ahmadq122/Digital-Weighing-Scale-6-Channel-MQTT/kicad/kicad-weight-scale-6-ch-rev_1.1-1.0/png/INALAB-full-wh.png

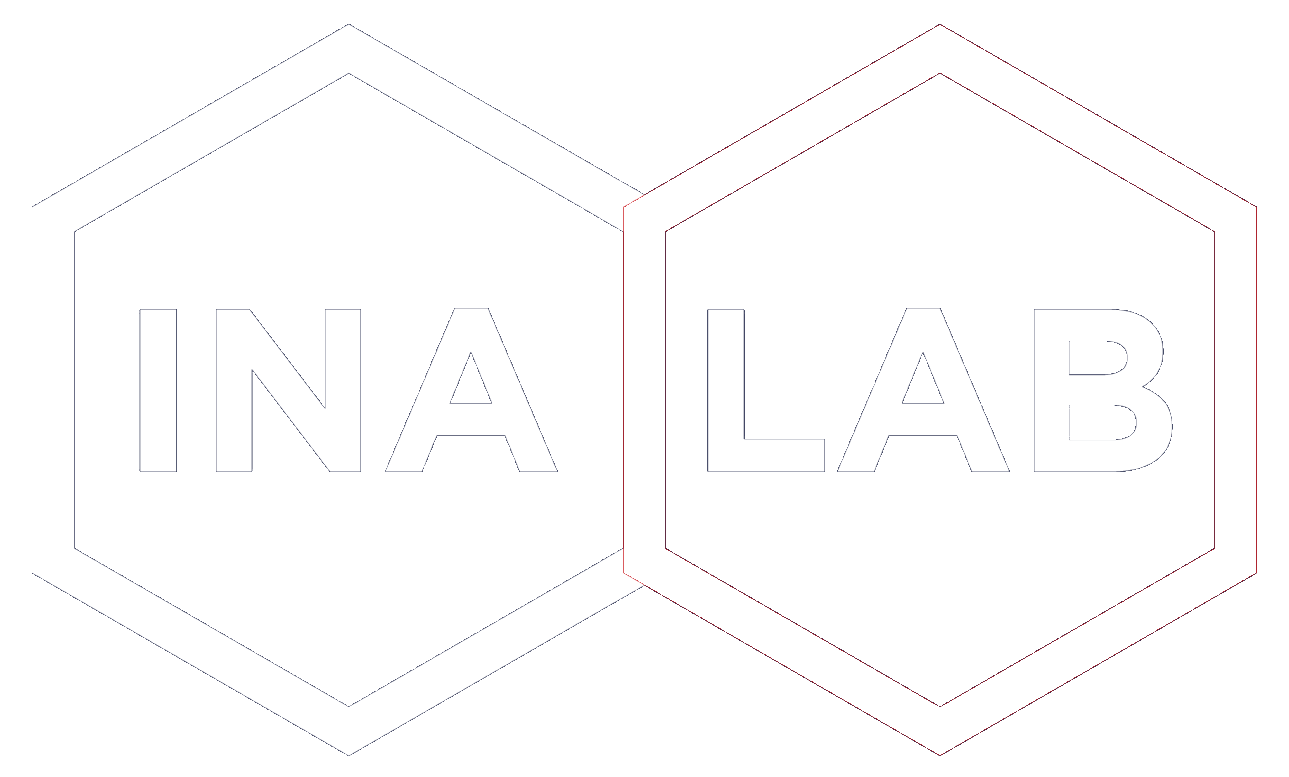
kicad/kicad-weight-scale-6-ch-rev_1.1-1.0/png/INALAB-full-wh.png
