ahmadq122/Digital-Weighing-Scale-6-Channel-MQTT/kicad/kicad-weight-scale-6-ch-rev_1.1-1.0/png/kicad-weight-scale-6-ch_top.png

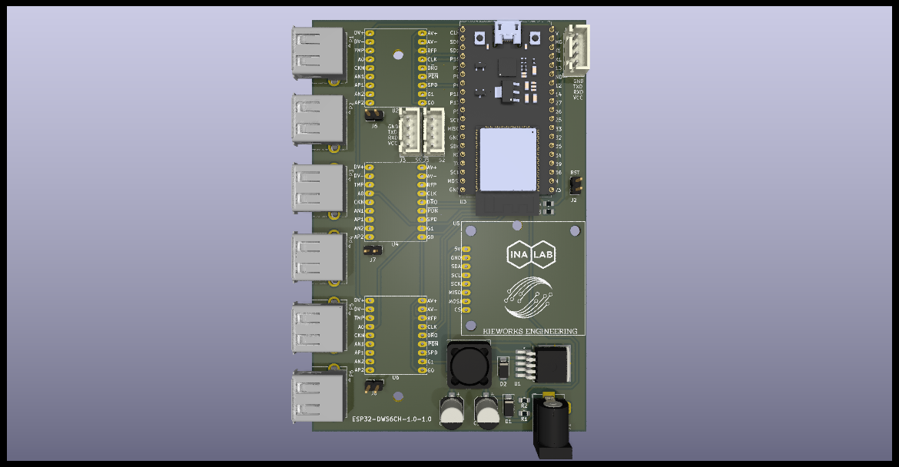
kicad/kicad-weight-scale-6-ch-rev_1.1-1.0/png/kicad-weight-scale-6-ch_top.png
