ahmadq122/Digital-Weighing-Scale-6-Channel-MQTT/src/Network/Network.cpp

#include "Network.h"
#include <WiFi.h>
#include "../FlashMemory/FlashMemory.h"
#include "../Nextion/Nextion.h"
#include "RTOS/RTOS.h"
#include "PictureListID.h"
#include "Utility/Utility.h"

void Network::setup(void)
{
    // Set WiFi to station mode and disconnect from an AP if it was previously connected
    // fdata->readAll();
    WiFi.mode(WIFI_STA);
    WiFi.disconnect();
    delay(100);
    if (fdata->getNetworkEnable())
    {
        WiFi.begin(fdata->getSSID(), fdata->getPassword());
        // WiFi.setAutoReconnect(true);
    }
    // Serial.println("Wifi Setup done");
}

const char *getStringEncrypt(byte parameter)
{
    if (parameter == 0)
        return "OPEN";
    else if (parameter == 1)
        return "WEP";
    else if (parameter == 2)
        return "WPA_PSK";
    else if (parameter == 3)
        return "WPA2_PSK";
    else if (parameter == 4)
        return "WPA_WPA2_PSK";
    else if (parameter == 5)
        return "WPA2_ENTERPRISE";
    else if (parameter == 6)
        return "MAX";
    else
        return "UNKNOWN";
}

char *getIPAdderss(void)
{
    static char buffer[30];
    // String ip;
    sprintf(buffer, "%s.%s.%s.%s", String(WiFi.localIP()[0]).c_str(), String(WiFi.localIP()[1]).c_str(), String(WiFi.localIP()[2]).c_str(), String(WiFi.localIP()[3]).c_str());
    // ip = String() + WiFi.localIP()[0] + "." + WiFi.localIP()[1] + "." + WiFi.localIP()[2] + "." + WiFi.localIP()[3];
    return buffer;
}

char *getStringPasswordMask(const char *string)
{
    char buffer[20];
    strcpy(buffer, string);
    // String str = string;
    uint8_t length = 0; // str.length();
    uint8_t i = 0;
    while (buffer[i] != '\0')
    {
        length++;
        i++;
    }

    static char mask[20];
    for (i = 0; i < length; i++)
        mask[i] = '*';
    mask[length] = '\0';
    return mask;
}

void Network::showNetworkProperty(bool flag)
{
    char buffer[50];
    if (flag)
    {
        for (uint8_t i = 1; i <= 6; i++)
        {
            sprintf(buffer, "q%d", i);
            hmi->setVisObjectNextion(buffer, true);
            sprintf(buffer, "t%d", i);
            hmi->setVisObjectNextion(buffer, true);
            delay(20);
            sprintf(buffer, "t%d.txt", i);
            if (i == 1)
            {
                hmi->setStringToNextion(buffer, WiFi.isConnected() ? "Connected" : "Unconnected");
            }
            else if (i == 2)
            {
                hmi->setStringToNextion(buffer, fdata->getSSID());
            }
            else if (i == 3)
            {
                hmi->setStringToNextion(buffer, utils.integerToString(WiFi.RSSI()));
            }
            else if (i == 4)
            {
                hmi->setStringToNextion(buffer, getIPAdderss());
            }
            else if (i == 5)
            {
                hmi->setStringToNextion(buffer, getStringEncrypt(fdata->getEncryptType()));
            }
            else if (i == 6)
            {
                hmi->setStringToNextion(buffer, getStringPasswordMask(fdata->getPassword()));
            }
        }
    }
    else
    {
        for (uint8_t i = 1; i <= 6; i++)
        {
            sprintf(buffer, "q%d", i);
            hmi->setVisObjectNextion(buffer, false);
            sprintf(buffer, "t%d", i);
            hmi->setVisObjectNextion(buffer, false);
        }
    }
}

bool Network::networkConfig(void)
{
    uint8_t button;
    bool netEnDis = false;
    bool needToRefreshStatus = false;

    hmi->showPage("netconf");
    hmi->waitForPageRespon();

    netEnDis = fdata->getNetworkEnable();

    hmi->setIntegerToNextion("b1.val", netEnDis);

    while (!hmi->getExitPageFlag())
    {
        if (!WiFi.isConnected() && netEnDis)
        {
            needToRefreshStatus = true;
            WiFi.begin(fdata->getSSID(), fdata->getPassword());
            // Serial.println(String() + "Connecting to " + fdata->getSSID());
        }
        if (fdata->getNetworkEnable())
        {
            hmi->setVisObjectNextion("b2", true);
            showNetworkProperty(true);
        }
        else
        {
            hmi->setVisObjectNextion("b2", false);
            showNetworkProperty(false);
        }
        // Wait for button press
        while (!hmi->checkAnyButtonPressed(&button))
        {
            // hmi->serialEvent_2();
            // delay(10);
            if (needToRefreshStatus && (WiFi.isConnected()))
            {
                showNetworkProperty(true);
                needToRefreshStatus = false;
            }
        }
        if (hmi->getDataButton(1))
        {
            netEnDis = !netEnDis;
            fdata->setNetworkEnable(netEnDis);
            hmi->setIntegerToNextion("b1.val", netEnDis);
            if (!netEnDis)
            {
                if (WiFi.isConnected())
                {
                    WiFi.disconnect();
                    // Serial.println("Network disconnected!");
                }
            }
        }
        else if (hmi->getDataButton(2))
        {
            return true;
        }
    }
    return false; // entering the scanning page;
}

void Network::networkScanning(void)
{
    uint8_t counterScan = 0;
    String ssidScanned[3][10];
    int rssiScanned[3][10];
    uint8_t encryptType[3][10];
    uint8_t numberOfNetworkFound[3];
    uint8_t selectedScan = 0, prevNoScan = 0;
    uint8_t progress = 0;
    String str;
    uint8_t button;
    char buffer[30];

    hmi->showPage("netscan");
    hmi->waitForPageRespon();
    // Serial.println("Network Scan page opened");
    WiFi.mode(WIFI_STA);
    WiFi.disconnect();

__scan:
    hmi->setIntegerToNextion("scan.val", progress);
    hmi->setVisObjectNextion("scan", true);
    counterScan = 0;
    while (counterScan < 3)
    {
        progress += 15;
        hmi->setIntegerToNextion("scan.val", progress);
        numberOfNetworkFound[counterScan] = WiFi.scanNetworks();
        for (uint8_t i = 0; i < numberOfNetworkFound[counterScan]; i++)
        {
            ssidScanned[counterScan][i] = WiFi.SSID(i);
            rssiScanned[counterScan][i] = WiFi.RSSI(i);
            encryptType[counterScan][i] = WiFi.encryptionType(i);
        }
        delay(2000);
        progress += 15;
        hmi->setIntegerToNextion("scan.val", progress);
        selectedScan = prevNoScan >= numberOfNetworkFound[counterScan] ? selectedScan : counterScan;
        prevNoScan = numberOfNetworkFound[counterScan];
        counterScan++;
        delay(1000);
    }

    delay(250);
    progress = 100;
    hmi->setIntegerToNextion("scan.val", progress);
    delay(250);
    hmi->setVisObjectNextion("scan", false);

    hmi->flushAvailableSerial();

    if (numberOfNetworkFound[selectedScan] == 0)
    {
        hmi->setStringToNextion("nonet.txt", "No Network Found!");
        hmi->setVisObjectNextion("nonet", true);
        // Serial.println("No network found!");
        while (!hmi->getExitPageFlag())
        {
            while (!hmi->checkAnyButtonPressed(&button))
            {
            }
            if (hmi->getDataButton(0))
            {
                hmi->setVisObjectNextion("nonet", false);
                progress = 0;
                goto __scan;
            }
        }
    }
    else
    {
        showNetworkList(numberOfNetworkFound[selectedScan]);
        // Serial.println(String() + numberOfNetworkFound[selectedScan] + " Networks found");
        while (!hmi->getExitPageFlag())
        {
            for (int i = 0; i < numberOfNetworkFound[selectedScan]; ++i)
            {
                if (isStoredNetwork(ssidScanned[selectedScan][i].c_str()))
                    showSelectedNetworkIndicator(i, numberOfNetworkFound[selectedScan]);
                str = ssidScanned[selectedScan][i];
                str += ":";
                str += rssiScanned[selectedScan][i];
                // Serial.println(String() + (i + 1) + ". " + str);
                sprintf(buffer, "b%d.txt", i);
                hmi->setStringToNextion(buffer, str.c_str());
            }
            while (!hmi->checkAnyButtonPressed(&button))
            {
                // hmi->serialEvent_2();
                // //Serial.println("wait1");
            }

            if (hmi->getDataButton(button))
            {
                if (ssidScanned[selectedScan][button].length() < MAX_SSID_CHAR)
                {
                    if (fdata->setSSID(ssidScanned[selectedScan][button].c_str()))
                    {
                        showSelectedNetworkIndicator(button, numberOfNetworkFound[selectedScan]);
                        fdata->setEncryptType(encryptType[selectedScan][button]);
                        WiFi.mode(WIFI_STA);
                        WiFi.disconnect();
                        delay(100);
                    }
                    rtos->wifiConnected = checkConnection();
                    if (!rtos->wifiConnected)
                    {
                        hmi->showPage("keyboard");
                        hmi->waitForPageRespon();
                        hmi->setIntegerToNextion("kb_hide.val", 1);
                        hmi->setIntegerToNextion("kb_string.pw", 1);

                        button = 0;
                        while (!hmi->checkAnyButtonPressed(&button))
                        {
                        }
                        if (hmi->getDataButton(1))
                        {
                            fdata->setPassword(hmi->getDataString(0));
                        }
                        hmi->showPage("netscan");
                        hmi->waitForPageRespon();
                        showNetworkList(numberOfNetworkFound[selectedScan]);
                    }
                }
                else
                {
                    // char* nonet = "No Network Found";
                    hmi->setStringToNextion("nonet.txt", "Invalid SSID!");
                    hmi->setVisObjectNextion("nonet", true);
                    delay(2000);
                    hmi->setVisObjectNextion("nonet", false);
                    // Serial.println("SSID selected must be no more than 11 characters!");
                }
            }
        }
    }
}

void Network::showNetworkList(uint8_t noOfList)
{
    char buffer[10];
    if (noOfList > 10)
        return;
    for (uint8_t i = 0; i < noOfList; i++)
    {
        sprintf(buffer, "b%d", i);
        hmi->setVisObjectNextion(buffer, true);
    }
    delay(500);
}

void Network::showSelectedNetworkIndicator(uint8_t selected, uint8_t noOfList)
{
    char buffer[20];
    if (noOfList > 10)
        return;
    sprintf(buffer, "b%d.picc", selected);
    hmi->setIntegerToNextion(buffer, Network_List_Select);
    for (uint8_t i = 0; i < noOfList; i++)
    {
        if (i == selected)
            continue;
        else
        {
            sprintf(buffer, "b%d.picc", i);
            hmi->setIntegerToNextion(buffer, Network_List_Bkg);
        }
    }
}

bool Network::isStoredNetwork(const char *networkName)
{
    if (!strcmp(networkName, fdata->getSSID()))
        return true;
    else
        return false;
}

bool Network::checkConnection(void)
{
    String ssid = fdata->getSSID();
    String password = fdata->getPassword();
    uint8_t counter = 0;
    if (ssid == "" || password == "")
    {
        return false;
    }

    if (!fdata->getNetworkEnable())
    {
        return false;
    }

    if (WiFi.isConnected())
    {
        // Serial.println("Network connected!");
    }
    else
    {
        // Serial.println("Network connection failed!");
        WiFi.begin(fdata->getSSID(), fdata->getPassword());
        while (!WiFi.isConnected() && counter <= 10)
        {
            delay(100);
            counter++;
        }
        if (WiFi.isConnected())
        {
            // Serial.println("Network connected!");
        }
    }
    return WiFi.isConnected();
}

bool Network::checkConnection(uint8_t *wifiSignal, bool *wifiConnectionTriggered)
{
    String ssid = fdata->getSSID();
    String password = fdata->getPassword();
    if (ssid == "" || password == "")
    {
        return false;
        // fdata->readAll();
    }

    bool connection = false;

    if (!fdata->getNetworkEnable())
    {
        *wifiSignal = 0;
        *wifiConnectionTriggered = false;
        return false;
    }

    if (WiFi.isConnected())
    {
        connection = true;
        *wifiSignal = calculateRSSILevel(WiFi.RSSI());
        if (*wifiConnectionTriggered && previousConnectionState != true)
        {
            previousConnectionState = true;
            // Serial.println("Network connected!");
        }
    }
    else
    {
        *wifiSignal = 0;
        connection = false;
        if (*wifiConnectionTriggered && previousConnectionState != false)
        {
            previousConnectionState = false;
            // Serial.println("Network connection failed!");
        }
    }
    if (*wifiConnectionTriggered)
    {
        if (!connection)
        {
            WiFi.begin(fdata->getSSID(), fdata->getPassword());
        }
        *wifiConnectionTriggered = false;
    }
    return connection;
}
uint8_t Network::calculateRSSILevel(int value)
{
    if (value >= -50)
        return 100;
    else if (value >= -60)
        return 85;
    else if (value >= -70)
        return 65;
    else if (value >= -80)
        return 45;
    else if (value >= -95)
        return 25;
    else
        return 0;
}

Network *net = new (Network);
