ahmadq122/Digital-Weighing-Scale-6-Channel-MQTT/src/ADC/ADS1232.h

#ifndef _ADS1232_H_
#define _ADS1232_H_

#include "Arduino.h"

#define SAMPLE_MOV_AVERAGE 40
#define ADC_OFFSET 100

#ifndef MAX_CHANNEL
#define MAX_CHANNEL 6
#endif

#define ERROR_WEIGHT 9999.999

enum Channel
{
    Channel1,
    Channel2,
    Channel3,
    Channel4,
    Channel5,
    Channel6
};
enum MeasurementUnits
{
    gram,       //1g
    milligram,  //1mg   = (1/0.001)g
    pound,      //1lb   = (1/453.59237)g
    ounce,      //1oz   = (1/28.34952)g
    troy_ounce, //1ozt  = (1/31.1034768)g
    carat,      //1ct   = (1/0.2)g
    kilogram,   //1kg   = (1/1000)g
    newton,     //1N    = (1/0.009807)g
    dram,       //1d    = (1/0.564383)g
    grain       //1GN   = (1/15.43236)g
};

enum BoardADS
{
    ads1,
    ads2,
    ads3
};

class ADS1232
{
public:
    uint32_t adcRead[3][2];     //ADC value after filtered
    String adcReadString[3][2]; ////ADC value convert to 10 characters of String
    void begin(void);
    bool init(uint8_t board);
    bool dataRead(uint8_t board, bool channel, bool calibrating);
    char* getStringWeightInUnit(uint8_t channel);
    char* getStringWeightInGram(uint8_t channel);
    float getWeightInGram(uint8_t channel);
    uint8_t PDWN;
    bool isAvailable[3];
    float tare[MAX_CHANNEL] = {0};
    bool enableTare[MAX_CHANNEL] = {false};
    float getWeightInUnit(byte channel);
    float dividerUnits[11] = {
        1,
        0.001,
        453.59237,
        28.34952,
        31.1034768,
        0.2,
        1000,
        0.009807,
        0.564383,
        15.43236};

private:
    // uint8_t PDWN[3];
    uint8_t SCLK[3];
    uint8_t DOUT[3];
    uint8_t A0[3];
    uint32_t adcBuffer[3][2][SAMPLE_MOV_AVERAGE];
    uint8_t index[3][2];
    uint8_t speed;

    bool prevChannel[3];

    bool dataReady(uint8_t board);
    unsigned char weightADCstate(unsigned long AdcValue, uint8_t channel);
    void setChannel(uint8_t board, uint8_t channel);
    void powerUp(void);
    void powerDown(void);
    uint8_t getPointDoneCalibrated(uint8_t pointCalibrationStatus);

    float weightCalculationInGram(unsigned long x1, float y1, unsigned long x2, float y2, unsigned long adcValue);
};

extern ADS1232* ads;

#endif
